fablabs-ch/nanobud/pictures/wiki/bad_weld.png

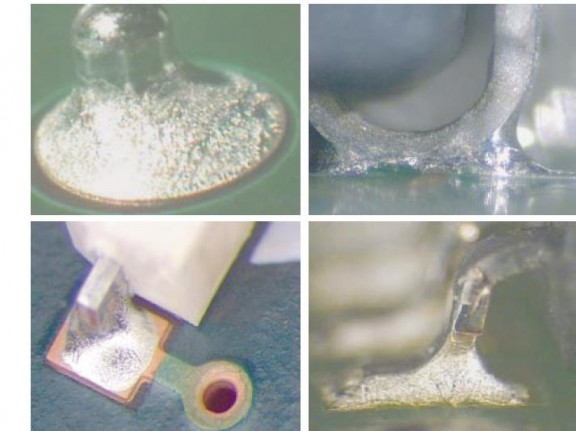
pictures/wiki/bad_weld.png
