fablabs-ch/nanobud/pictures/wiki/bad_weld_2.png

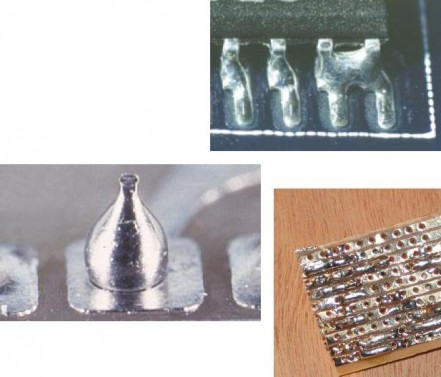
pictures/wiki/bad_weld_2.png
