fablabs-ch/nanobud/pictures/wiki/coupante.png

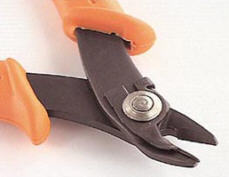
pictures/wiki/coupante.png
