fablabs-ch/nanobud/pictures/wiki/denudeur.png

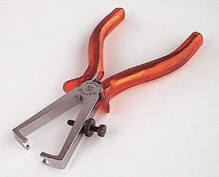
pictures/wiki/denudeur.png
