fablabs-ch/nanobud/pictures/wiki/flux.png

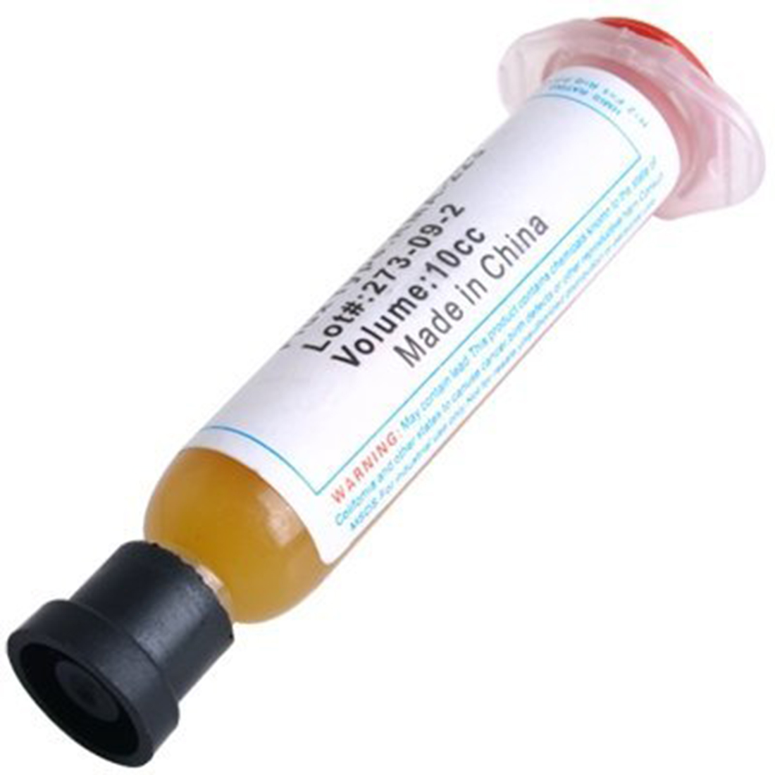
pictures/wiki/flux.png
