fablabs-ch/nanobud/pictures/wiki/good_weld.png

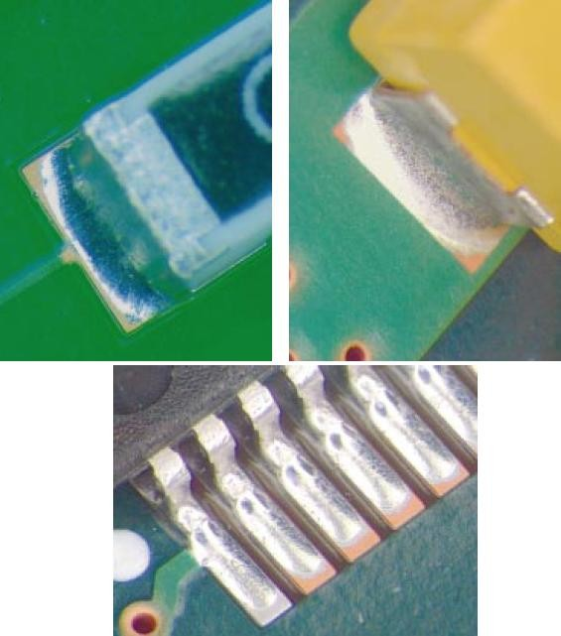
pictures/wiki/good_weld.png
