fablabs-ch/nanobud/pictures/wiki/gratte2.png

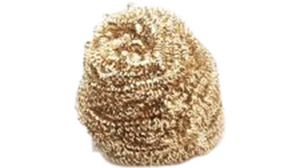
pictures/wiki/gratte2.png
