fablabs-ch/nanobud/pictures/wiki/gratte.png

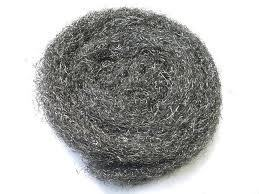
pictures/wiki/gratte.png
