fablabs-ch/nanobud/pictures/wiki/lead-free2.png

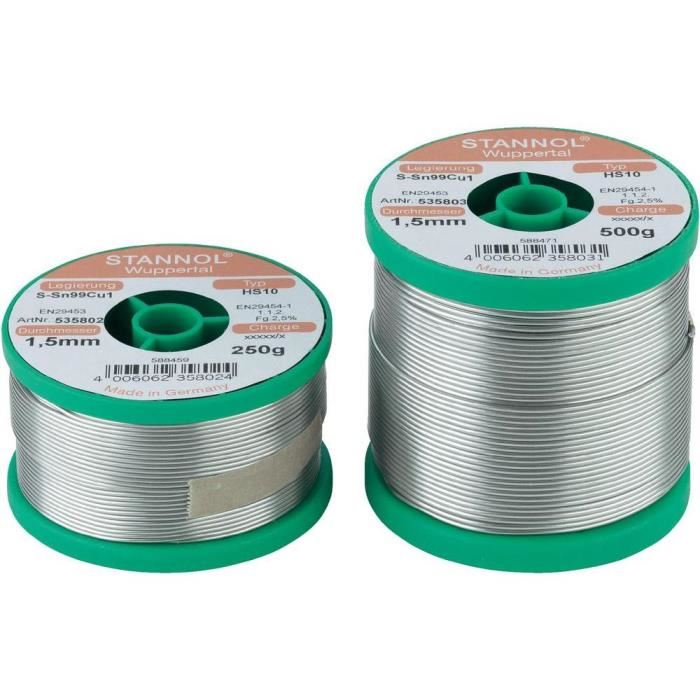
pictures/wiki/lead-free2.png
