fablabs-ch/nanobud/pictures/wiki/lead-free.png

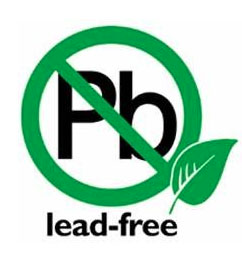
pictures/wiki/lead-free.png
