fablabs-ch/nanobud/pictures/wiki/longue.png

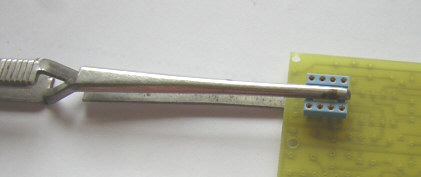
pictures/wiki/longue.png
