fablabs-ch/nanobud/pictures/wiki/paste.png

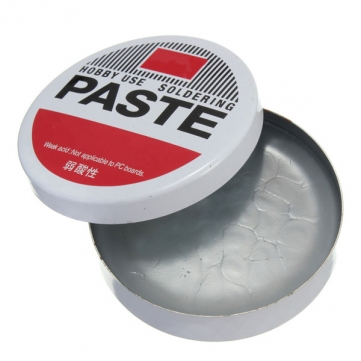
pictures/wiki/paste.png
