fablabs-ch/nanobud/pictures/wiki/pompe.png

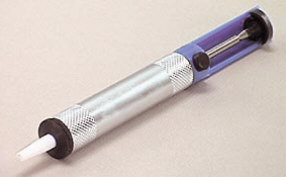
pictures/wiki/pompe.png
