fablabs-ch/nanobud/pictures/wiki/support.png

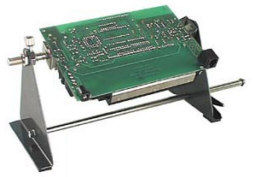
pictures/wiki/support.png
