fablabs-ch/nanobud/pictures/wiki/third_hand.png

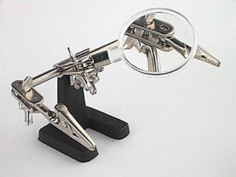
pictures/wiki/third_hand.png
