fablabs-ch/nanobud/pictures/wiki/tresse.png

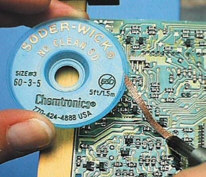
pictures/wiki/tresse.png
