fablabs-ch/nanobud/pictures/wiki/weld.png

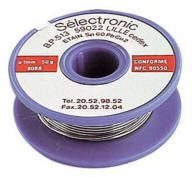
pictures/wiki/weld.png
