fablabs-ch/nanobud/pictures/wiki/weld_2.png

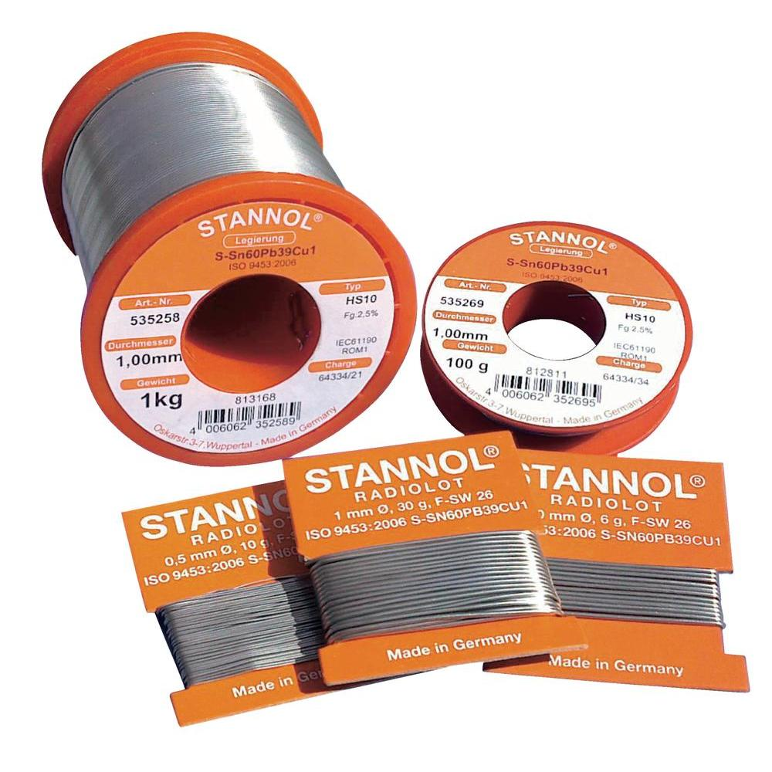
pictures/wiki/weld_2.png
