fablabs-ch/nanobud/pictures/wiki/welding_station2.png

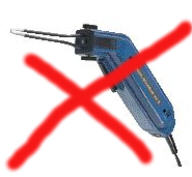
pictures/wiki/welding_station2.png
