fablabs-ch/nanobud/pictures/wiki/welding_station_1.png

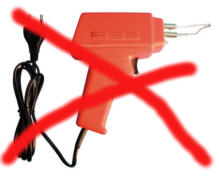
pictures/wiki/welding_station_1.png
