fablabs-ch/nanobud/pictures/wiki/welding_station_3.png

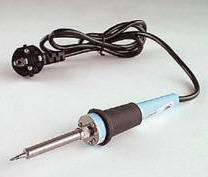
pictures/wiki/welding_station_3.png
