fablabs-ch/nanobud/pictures/wiki/welding_station_4.png

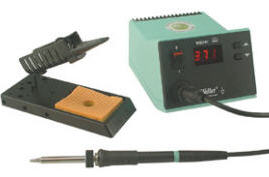
pictures/wiki/welding_station_4.png
