fablabs-ch/nanobud/pictures/wiki/welding_station_5.png

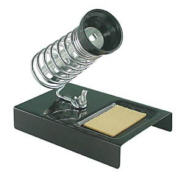
pictures/wiki/welding_station_5.png
