fablabs-ch/nanobud/pictures/wiki/welding_tip_2.png

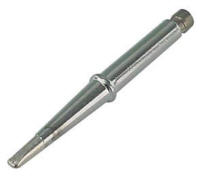
pictures/wiki/welding_tip_2.png
