fablabs-ch/nanobud/pictures/material.JPG

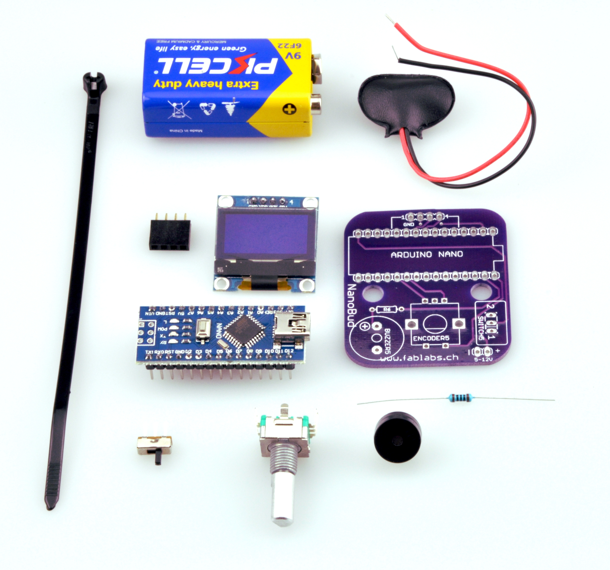
pictures/material.JPG
