fablabs-ch/nanobud/pictures/instructions_nanobud-page001.png

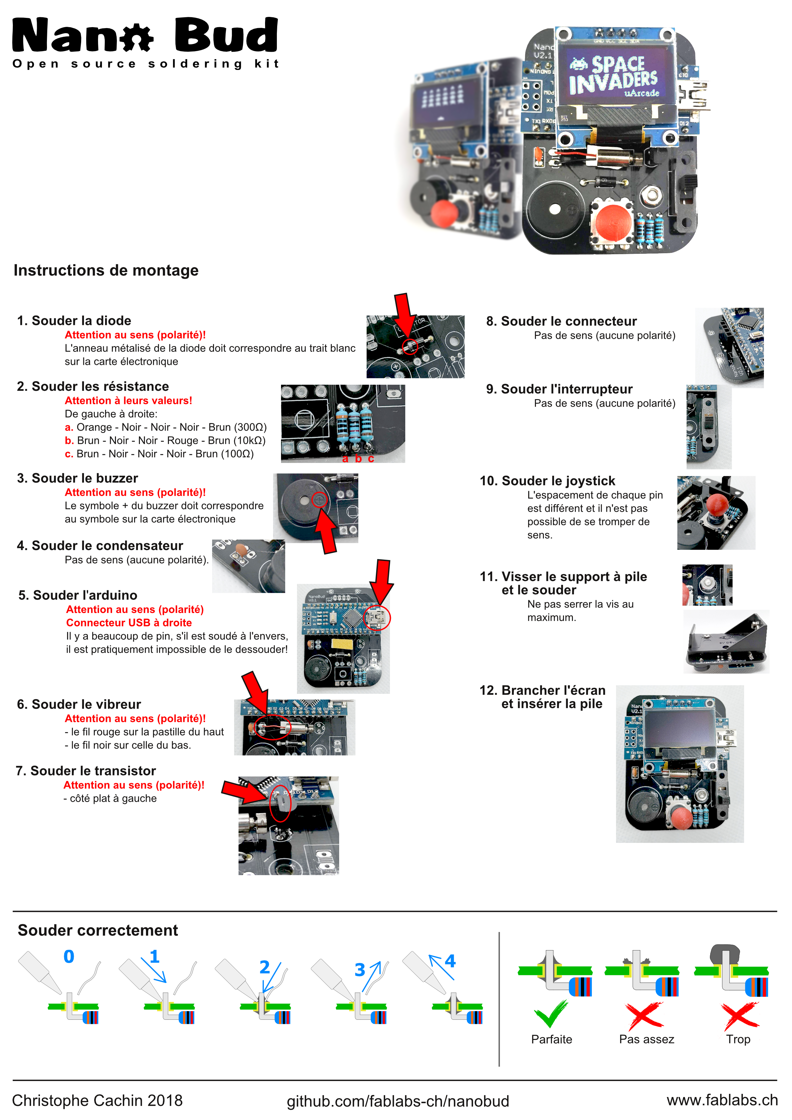
pictures/instructions_nanobud-page001.png
