fablabs-ch/nanobud/pictures/instructions_nanobud.png

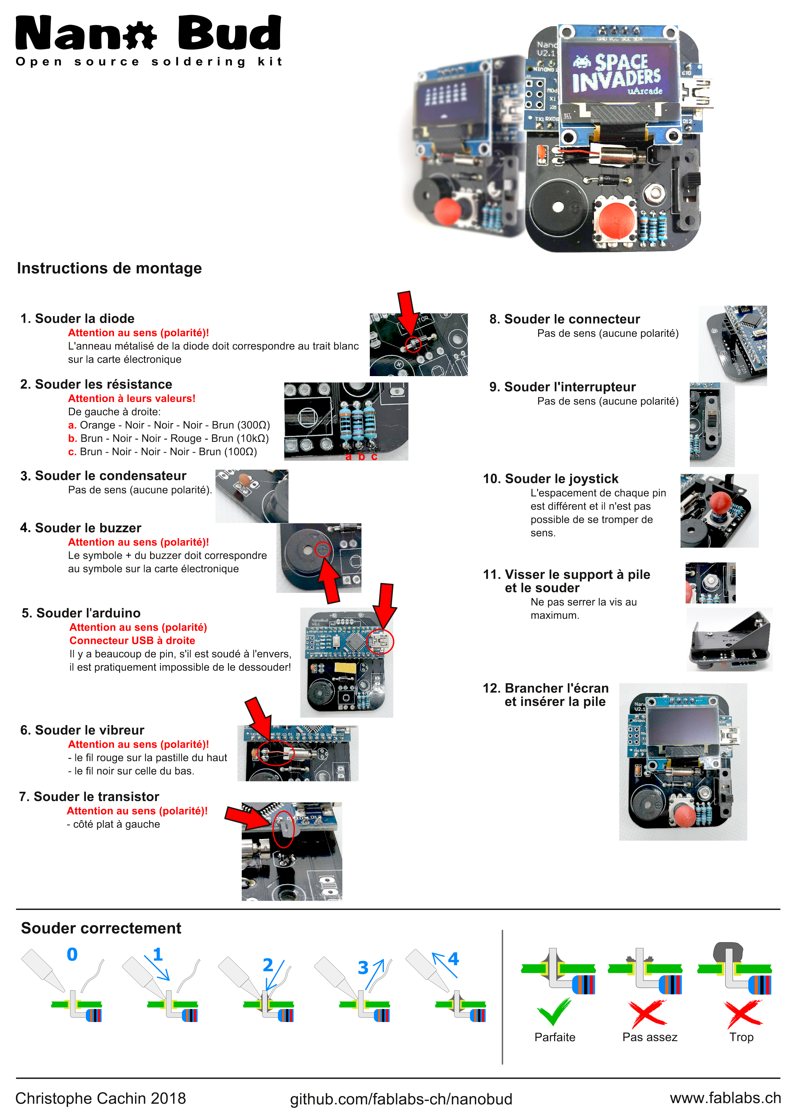
pictures/instructions_nanobud.png
